NazarDiadiun/ETS2-DAF-Dashboard/Microcontroller Code/ETS2_DAF_Code/Project_Functions.h

void Dashboard_Main_Callback();
void Right_Display_Callback();
void Icons_Callback();
void Speedometer_Callback();
void RPM_Callback();
void Distances_Callback();
void Arrows_Callback();
void Time_Callback();

void Mileage_Read_Callback();

byte SearchIcon(byte IconID, byte IconType);
bool ToggleIcon(byte IconID, byte IconType);
